technoez/open-makers-cube/assemblies/arduino_uno_mounting_plate_portrait_assembly.png

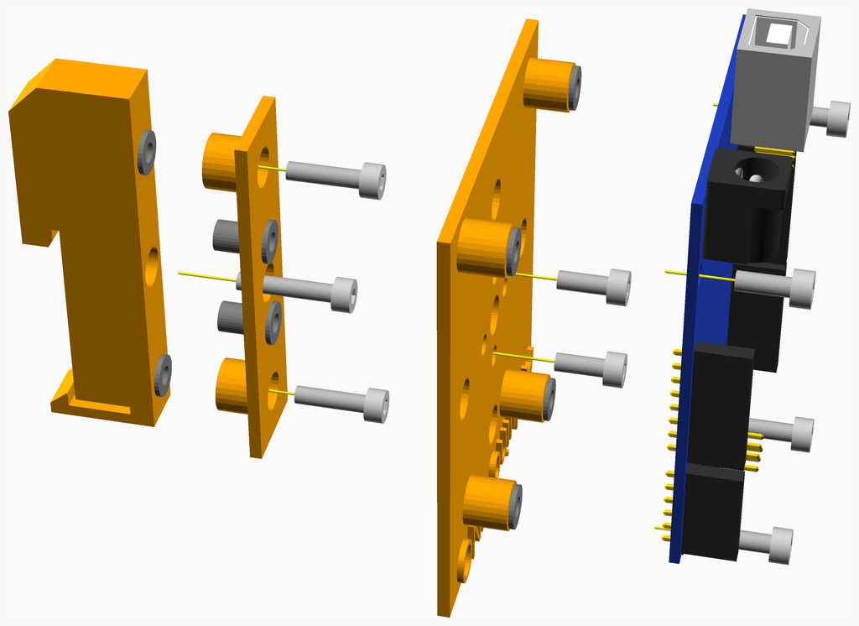
assemblies/arduino_uno_mounting_plate_portrait_assembly.png
