technoez/open-makers-cube/assemblies/back_spin_plate_assembled.png

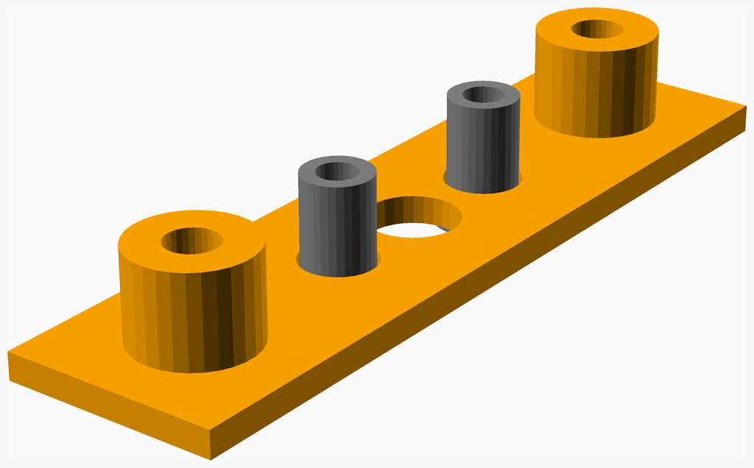
assemblies/back_spin_plate_assembled.png
