technoez/open-makers-cube/assemblies/back_spin_plate_assembly.png

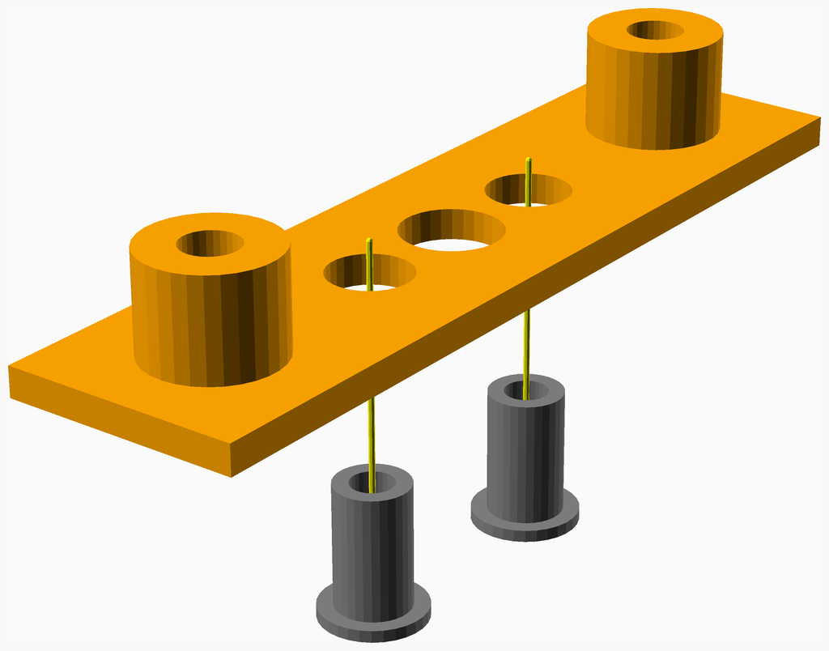
assemblies/back_spin_plate_assembly.png
