technoez/open-makers-cube/assemblies/carry_handle_assembly_tn.png

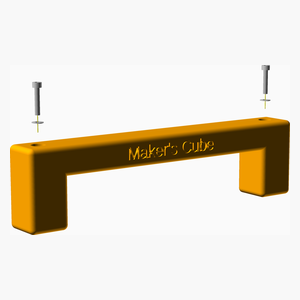
assemblies/carry_handle_assembly_tn.png
