technoez/open-makers-cube/assemblies/corner_lamp_holder_assembled.png

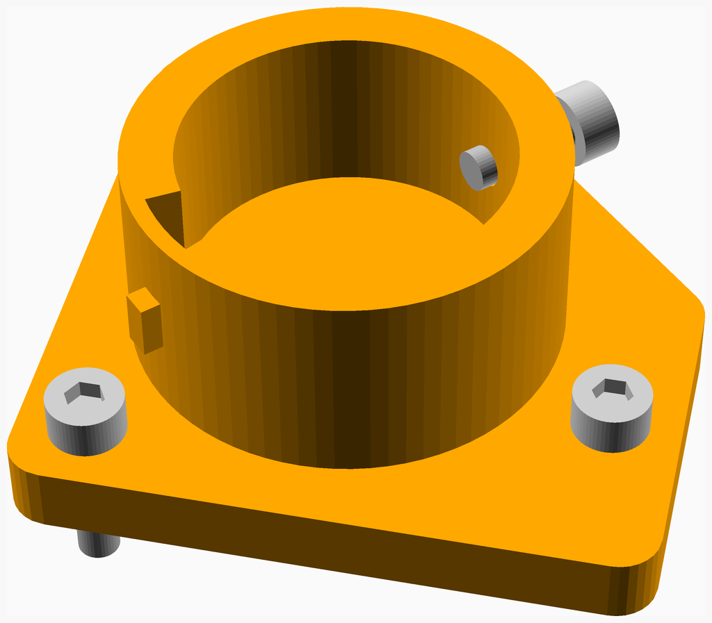
assemblies/corner_lamp_holder_assembled.png
