technoez/open-makers-cube/assemblies/corner_lamp_holder_assembly.png

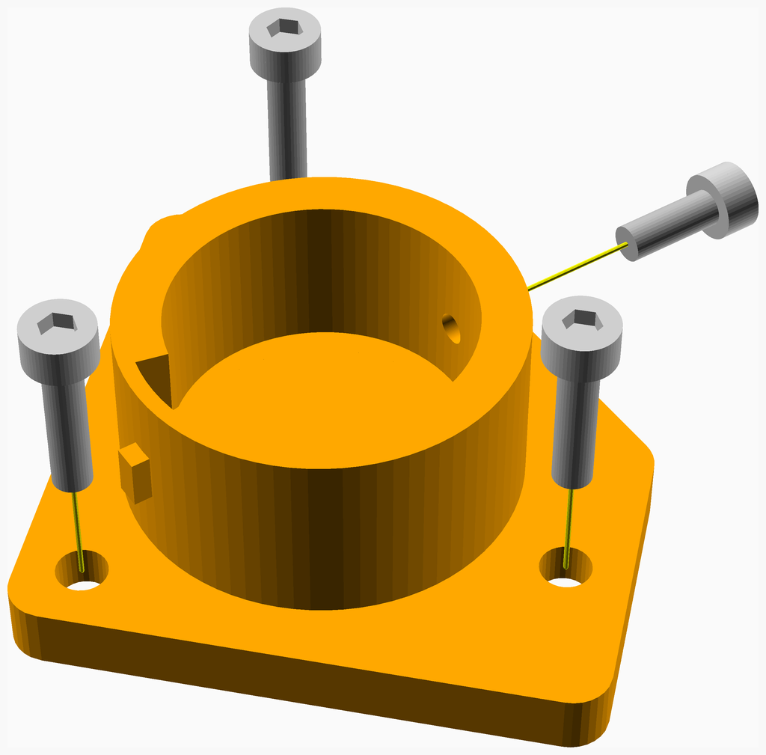
assemblies/corner_lamp_holder_assembly.png
