technoez/open-makers-cube/assemblies/corner_tube_top_assembly.png

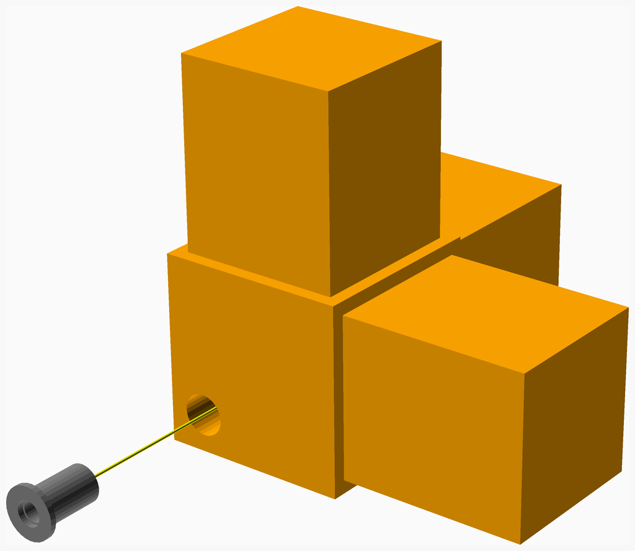
assemblies/corner_tube_top_assembly.png
