technoez/open-makers-cube/assemblies/din_rail_assembled.png

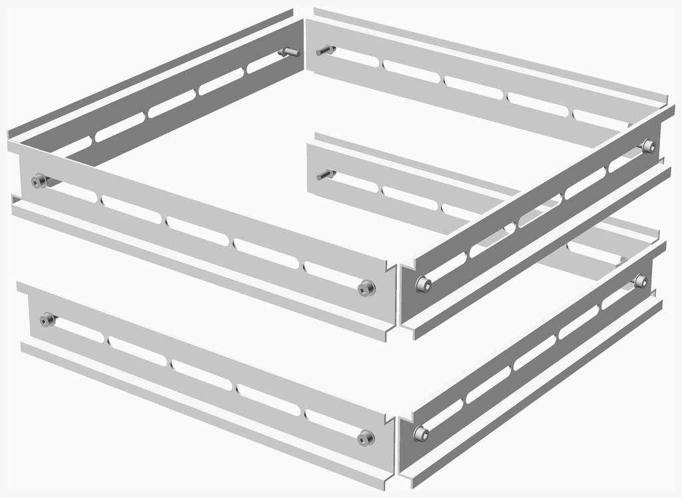
assemblies/din_rail_assembled.png
