technoez/open-makers-cube/assemblies/din_rail_assembly.png

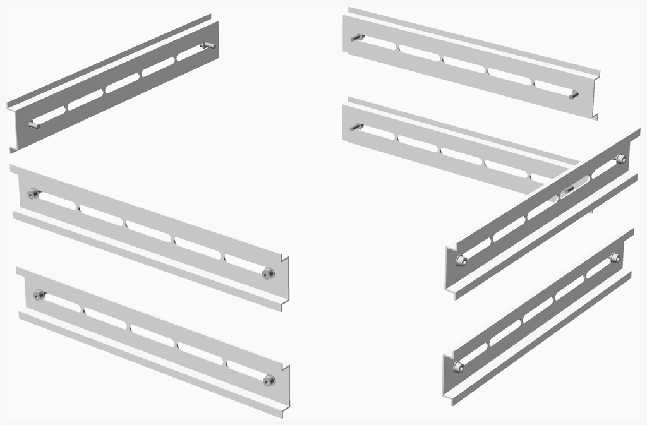
assemblies/din_rail_assembly.png
