technoez/open-makers-cube/assemblies/din_rail_clip_assembled.png

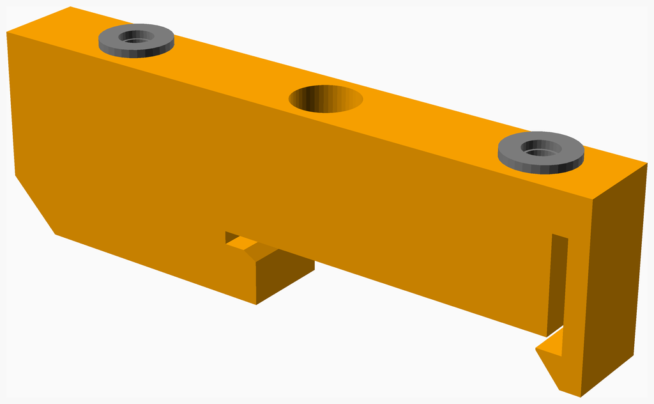
assemblies/din_rail_clip_assembled.png
