technoez/open-makers-cube/assemblies/din_rail_clip_assembly.png

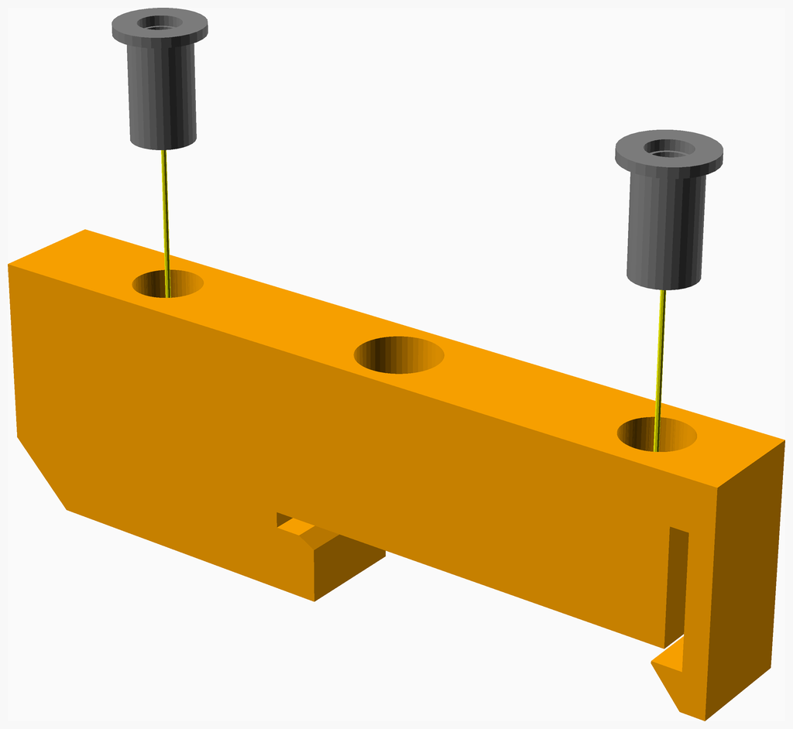
assemblies/din_rail_clip_assembly.png
