technoez/open-makers-cube/assemblies/frame_assembled.png

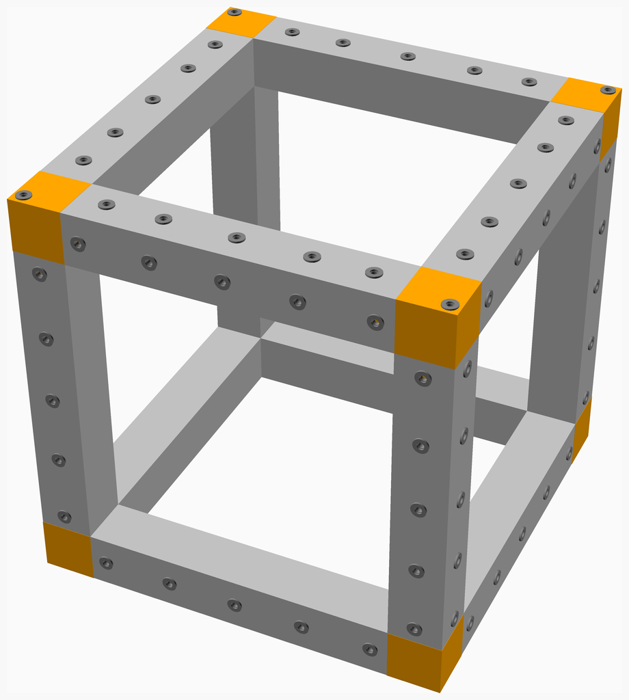
assemblies/frame_assembled.png
