technoez/open-makers-cube/assemblies/frame_assembly.png

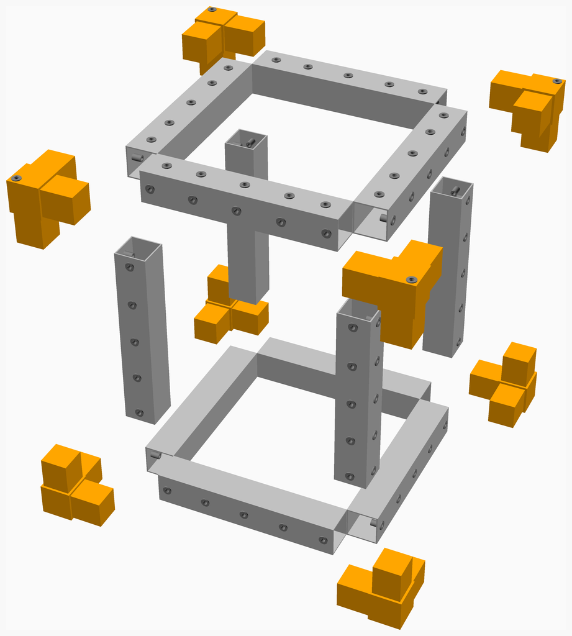
assemblies/frame_assembly.png
