technoez/open-makers-cube/assemblies/frame_bottom_assembled.png

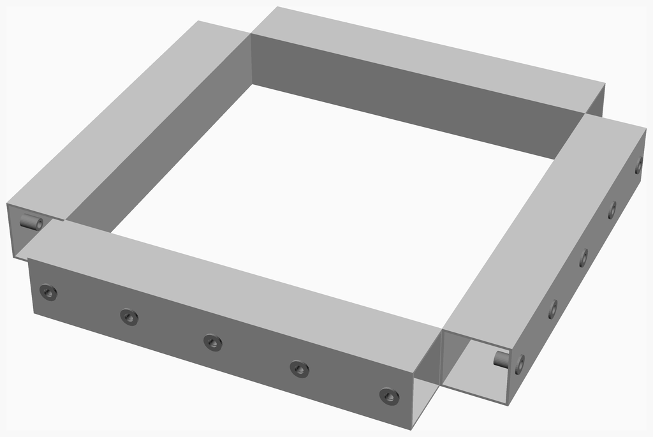
assemblies/frame_bottom_assembled.png
