technoez/open-makers-cube/assemblies/frame_bottom_assembly.png

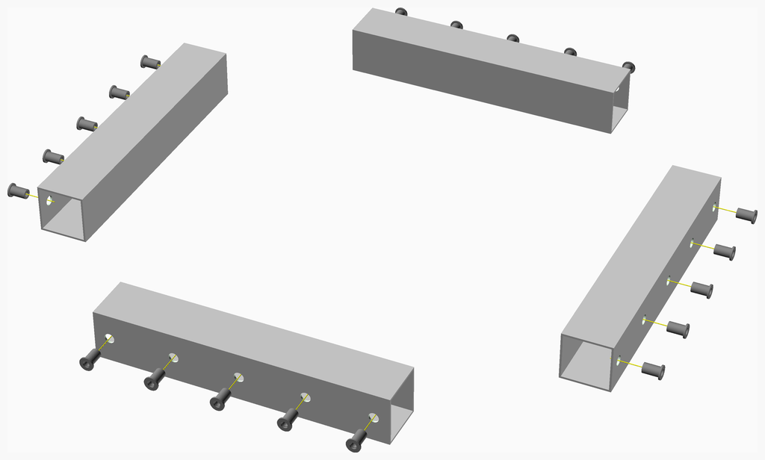
assemblies/frame_bottom_assembly.png
