technoez/open-makers-cube/assemblies/frame_middle_assembly.png

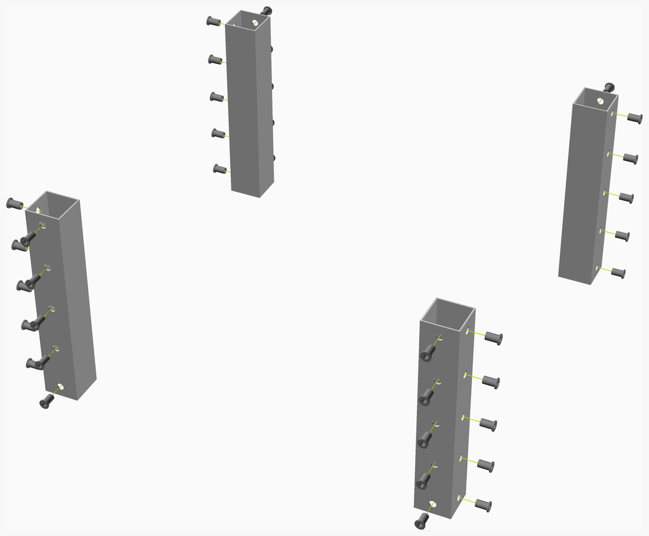
assemblies/frame_middle_assembly.png
