technoez/open-makers-cube/assemblies/frame_top_assembly.png

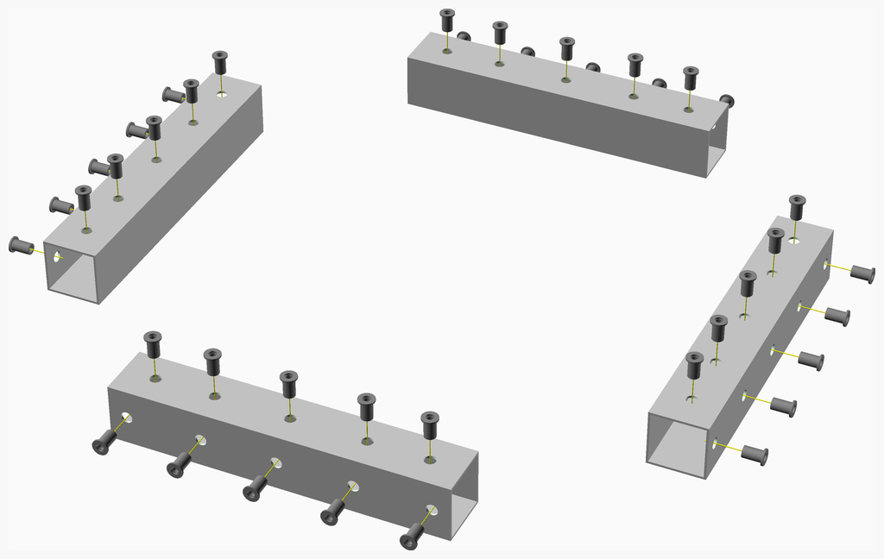
assemblies/frame_top_assembly.png
