technoez/open-makers-cube/assemblies/helping_hands_assembled.png

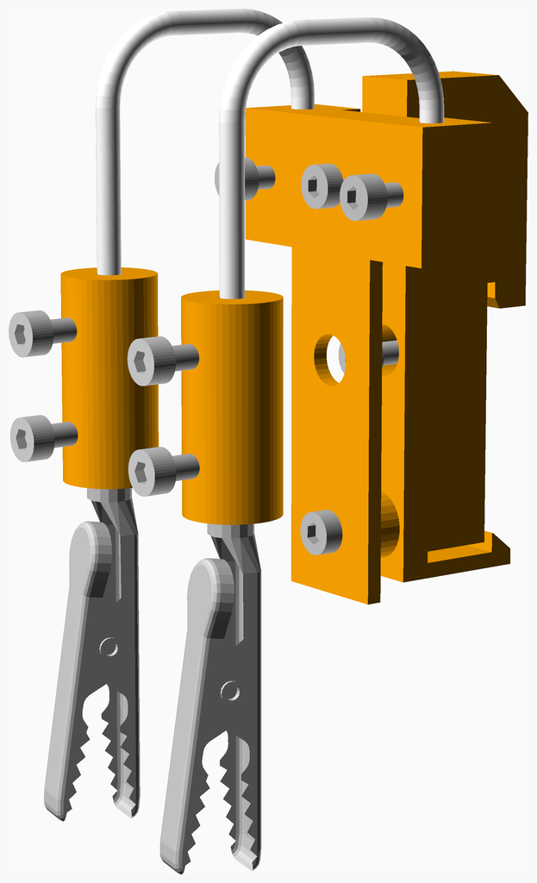
assemblies/helping_hands_assembled.png
