technoez/open-makers-cube/assemblies/helping_hands_assembly.png

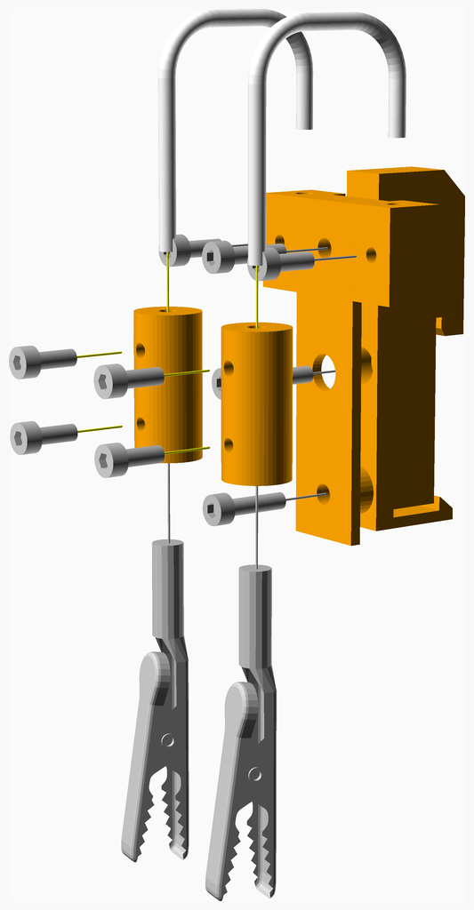
assemblies/helping_hands_assembly.png
