technoez/open-makers-cube/assemblies/main_assembled_tn.png

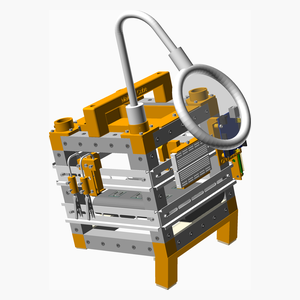
assemblies/main_assembled_tn.png
