technoez/open-makers-cube/assemblies/main_assembly_tn.png

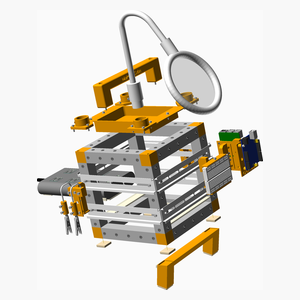
assemblies/main_assembly_tn.png
