technoez/open-makers-cube/assemblies/power_strip_assembled.png

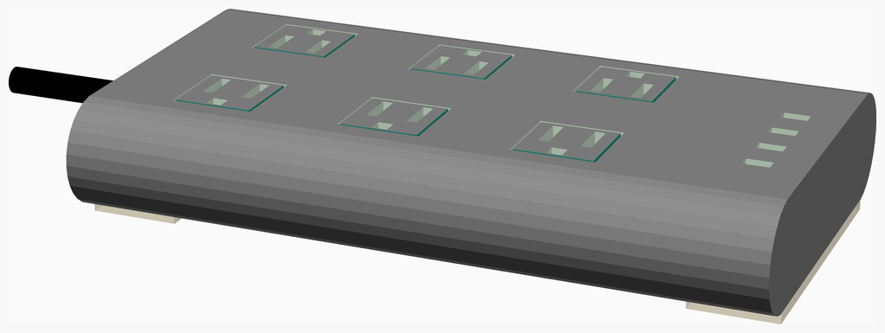
assemblies/power_strip_assembled.png
