technoez/open-makers-cube/assemblies/power_strip_assembly.png

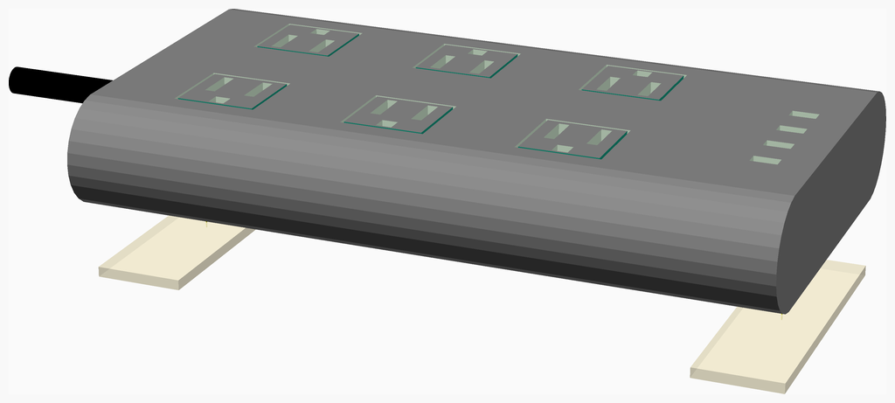
assemblies/power_strip_assembly.png
