technoez/open-makers-cube/assemblies/prop_assembly_tn.png

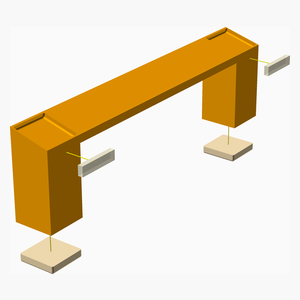
assemblies/prop_assembly_tn.png
