technoez/open-makers-cube/assemblies/raspberry_pi_mounting_plate_portrait_assembly.png

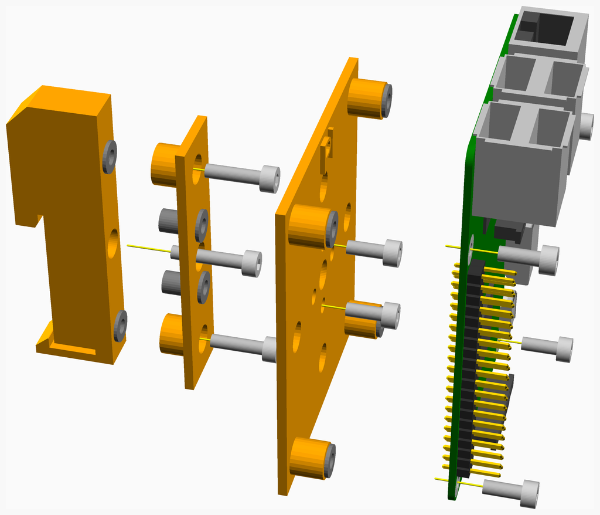
assemblies/raspberry_pi_mounting_plate_portrait_assembly.png
