technoez/open-makers-cube/assemblies/small_breadboard_portrait_assembled.png

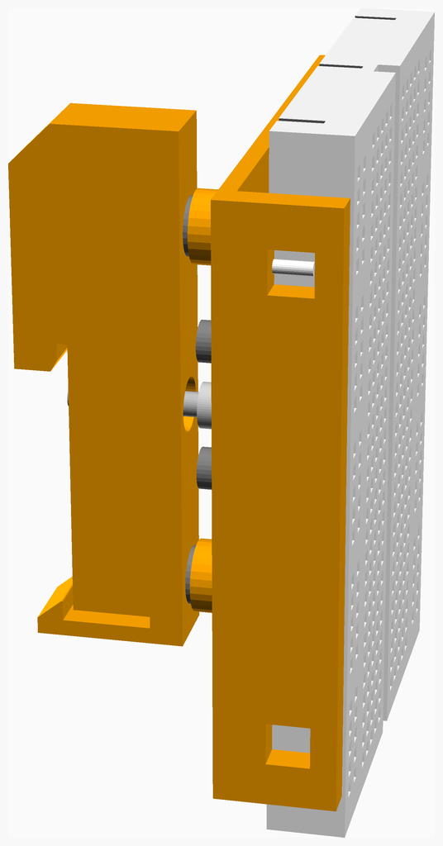
assemblies/small_breadboard_portrait_assembled.png
