technoez/open-makers-cube/assemblies/tray_assembled.png

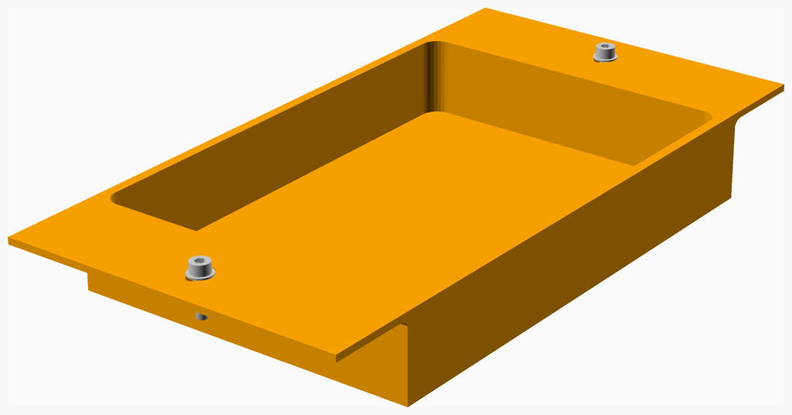
assemblies/tray_assembled.png
