technoez/open-makers-cube/assemblies/tray_assembly.png

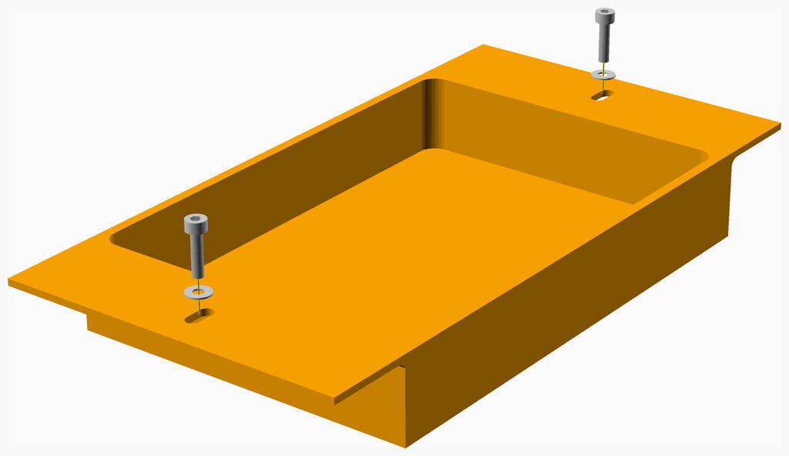
assemblies/tray_assembly.png
